NorthCoastModularCollective/Ann-Arbor-Percussion-Synthesizer/hardware/A2 Drums/A2 Drums.kicad_sch

## KiCad design hardware/A2 Drums/A2 Drums.kicad_sch (2023-11-15)

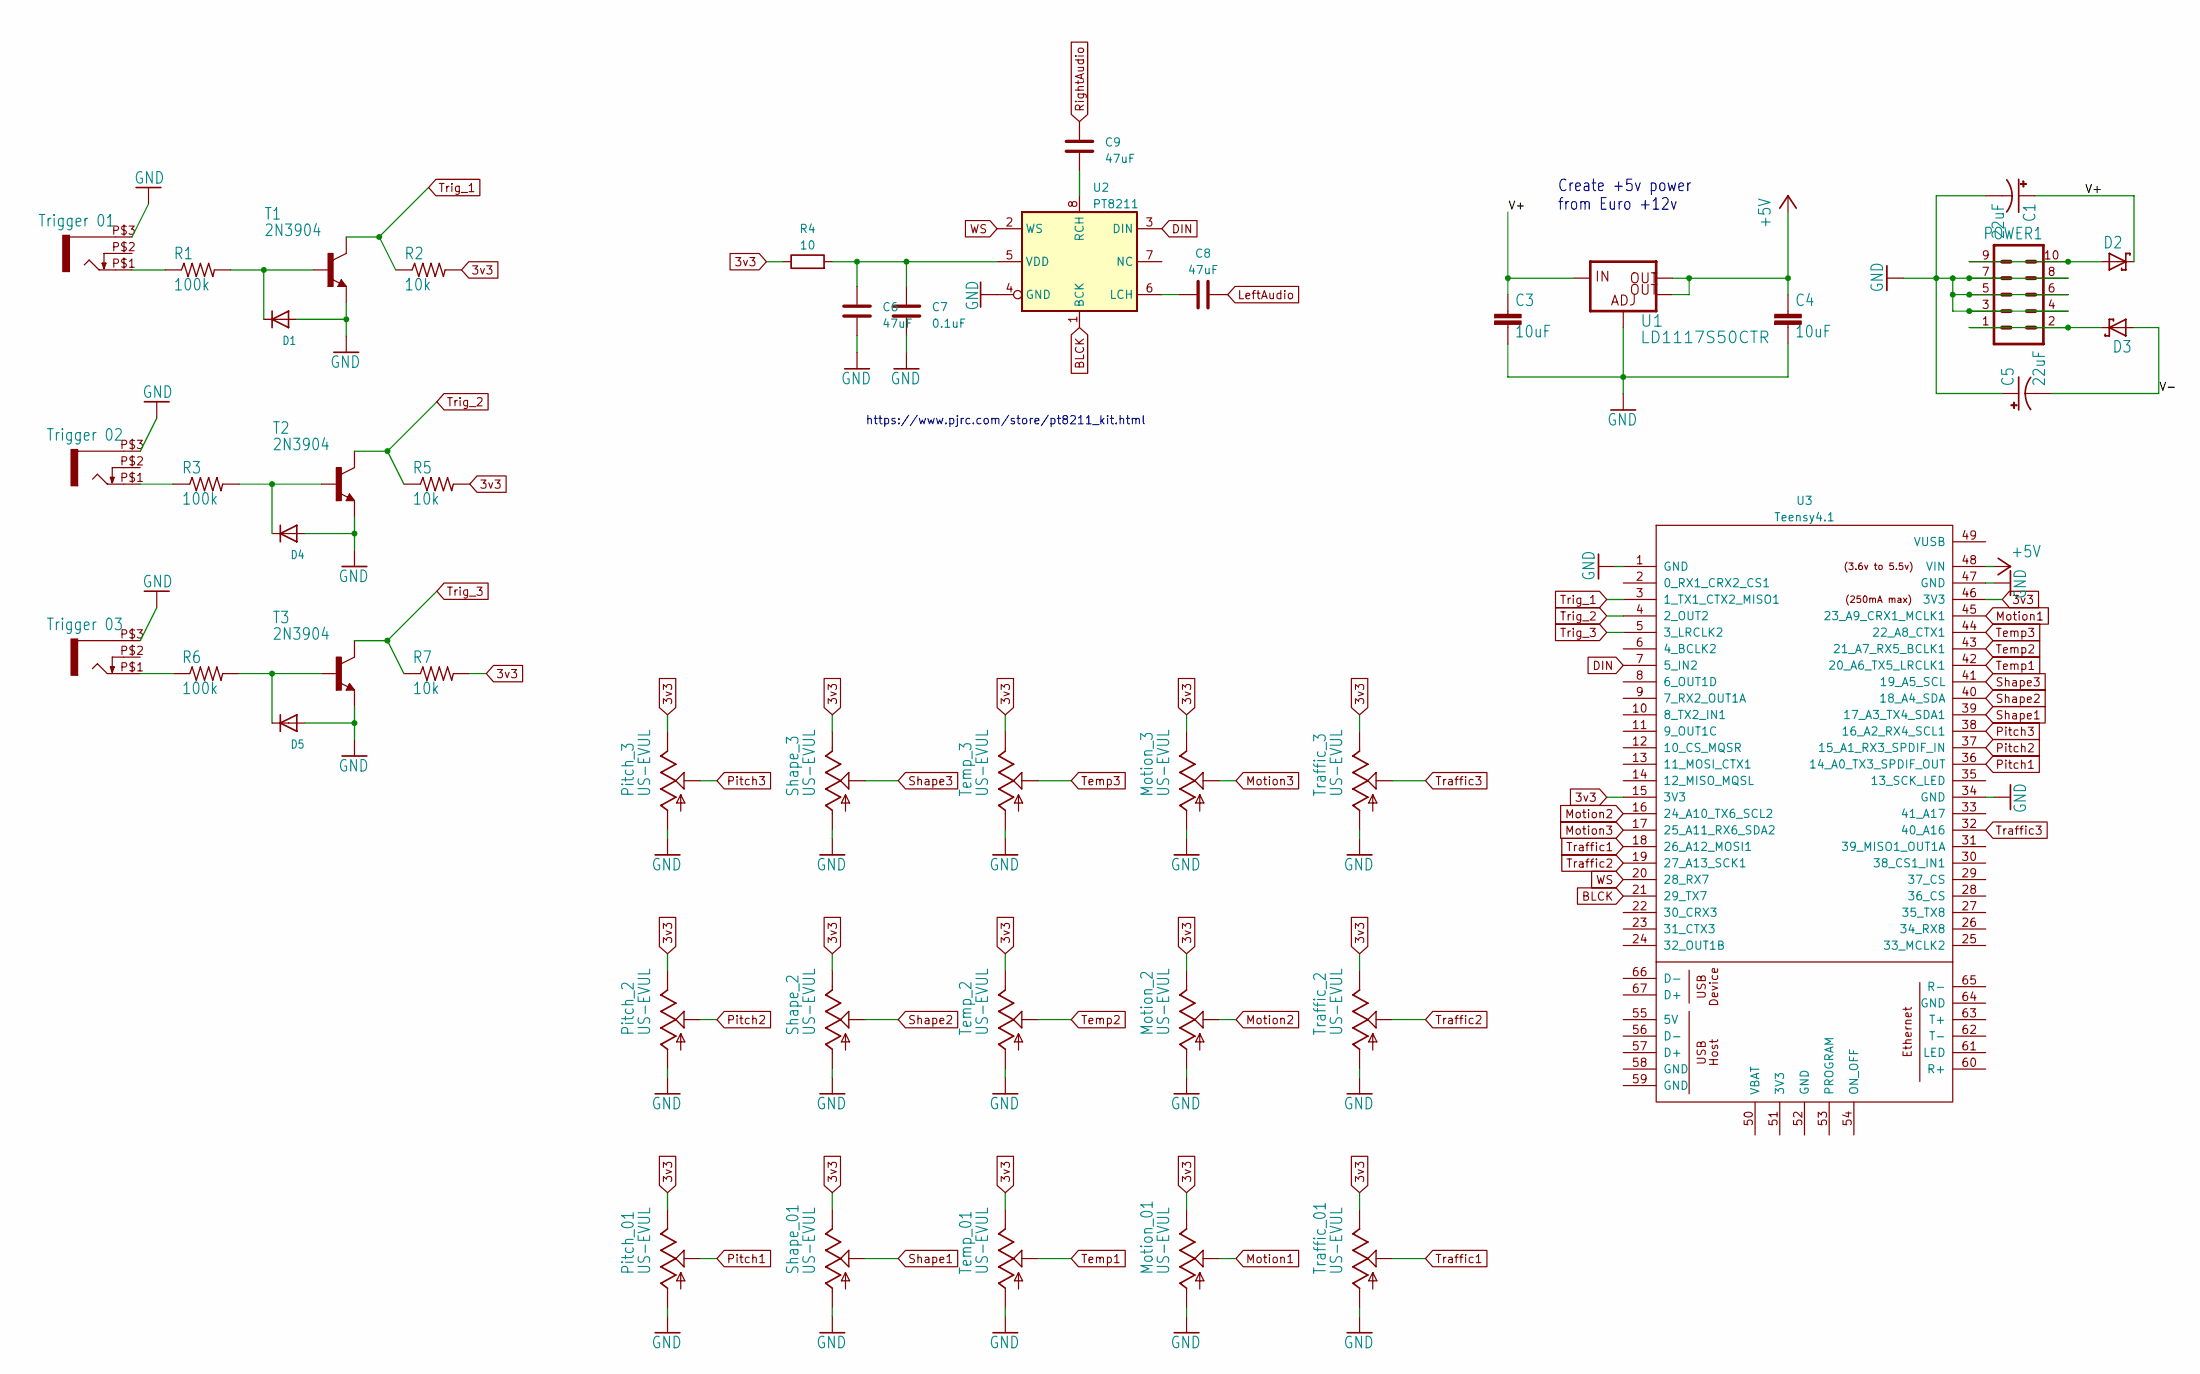
[picture p6: schematic A2 Drums.kicad_sch]

Parts:
C1, C5: 22uF; E2,5-5
C3, C4: 10uF; C5B2.5
C6, C8, C9: 47uF; C_Axial_L5.1mm_D3.1mm_P7.50mm_Horizontal
C7: 0.1uF; C_Axial_L5.1mm_D3.1mm_P7.50mm_Horizontal
D1, D4, D5: DIODESOD-123; SOD-123
D2, D3: SCHOTTKY-DIODEDO41; DO41-10
Motion_01, Motion_2, Motion_3: US-EVUL; EVUFXL
POWER1: MA05-2
Pitch_01, Pitch_2, Pitch_3: US-EVUL; EVUFXL
R1, R3, R6: 100k; R0805
R2, R5, R7: 10k; R0805
R4: 10; R_Axial_DIN0207_L6.3mm_D2.5mm_P7.62mm_Horizontal
Shape_01, Shape_2, Shape_3: US-EVUL; EVUFXL
T1, T2, T3: 2N3904; TO92
TRIG1: Trigger 01; WQP-PJ301M-12_JACK
TRIG2: Trigger 02; WQP-PJ301M-12_JACK
TRIG3: Trigger 03; WQP-PJ301M-12_JACK
Temp_01, Temp_2, Temp_3: US-EVUL; EVUFXL
Traffic_01, Traffic_2, Traffic_3: US-EVUL; EVUFXL
U1: LD1117S50CTR; SOT223
U2: PT8211; VSSOP-8_3.0x3.0mm_P0.65mm
U3: Teensy4.1

Connections:
3v3: Motion_01.3 (E), Motion_2.3 (E), Motion_3.3 (E), Pitch_01.3 (E), Pitch_2.3 (E), Pitch_3.3 (E), R2.2, R4.1, R5.2, R7.2, Shape_01.3 (E), Shape_2.3 (E), Shape_3.3 (E), Temp_01.3 (E), Temp_2.3 (E), Temp_3.3 (E), Traffic_01.3 (E), Traffic_2.3 (E), Traffic_3.3 (E), U3.15 (3V3), U3.46 (3V3)
+5V: C4.1, U1.2 (OUT), U1.4 (OUT@1), U3.48 (VIN)
BLCK: U2.1 (BCK), U3.21 (29_TX7)
DIN: U2.3 (DIN), U3.7 (5_IN2)
GND: C1.-, C3.2, C4.2, C5.+, C6.2, C7.2, D1.A, D4.A, D5.A, Motion_01.1 (A), Motion_2.1 (A), Motion_3.1 (A), POWER1.3, POWER1.4, POWER1.5, POWER1.6, POWER1.7, POWER1.8, Pitch_01.1 (A), Pitch_2.1 (A), Pitch_3.1 (A), Shape_01.1 (A), Shape_2.1 (A), Shape_3.1 (A), T1.3 (E), T2.3 (E), T3.3 (E), TRIG1.P$3 (1), TRIG2.P$3 (1), TRIG3.P$3 (1), Temp_01.1 (A), Temp_2.1 (A), Temp_3.1 (A), Traffic_01.1 (A), Traffic_2.1 (A), Traffic_3.1 (A), U1.1 (ADJ), U2.4 (GND), U3.1 (GND), U3.34 (GND), U3.47 (GND)
LeftAudio: C8.2
Motion1: Motion_01.2 (S), U3.45 (23_A9_CRX1_MCLK1)
Motion2: Motion_2.2 (S), U3.16 (24_A10_TX6_SCL2)
Motion3: Motion_3.2 (S), U3.17 (25_A11_RX6_SDA2)
unnamed: C6.1, C7.1, R4.2, U2.5 (VDD)
unnamed: C8.1, U2.6 (LCH)
unnamed: C9.1, U2.8 (RCH)
unnamed: D1.C, R1.2, T1.2 (B)
unnamed: D2.A, POWER1.9, POWER1.10
unnamed: D3.C, POWER1.1, POWER1.2
unnamed: D4.C, R3.2, T2.2 (B)
unnamed: D5.C, R6.2, T3.2 (B)
unnamed: R1.1, TRIG1.P$1 (2)
unnamed: R3.1, TRIG2.P$1 (2)
unnamed: R6.1, TRIG3.P$1 (2)
Pitch1: Pitch_01.2 (S), U3.36 (14_A0_TX3_SPDIF_OUT)
Pitch2: Pitch_2.2 (S), U3.37 (15_A1_RX3_SPDIF_IN)
Pitch3: Pitch_3.2 (S), U3.38 (16_A2_RX4_SCL1)
RightAudio: C9.2
Shape1: Shape_01.2 (S), U3.39 (17_A3_TX4_SDA1)
Shape2: Shape_2.2 (S), U3.40 (18_A4_SDA)
Shape3: Shape_3.2 (S), U3.41 (19_A5_SCL)
Temp1: Temp_01.2 (S), U3.42 (20_A6_TX5_LRCLK1)
Temp2: Temp_2.2 (S), U3.43 (21_A7_RX5_BCLK1)
Temp3: Temp_3.2 (S), U3.44 (22_A8_CTX1)
Traffic1: Traffic_01.2 (S), U3.18 (26_A12_MOSI1)
Traffic2: Traffic_2.2 (S), U3.19 (27_A13_SCK1)
Traffic3: Traffic_3.2 (S), U3.32 (40_A16)
Trig_1: R2.1, T1.1 (C), U3.3 (1_TX1_CTX2_MISO1)
Trig_2: R5.1, T2.1 (C), U3.4 (2_OUT2)
Trig_3: R7.1, T3.1 (C), U3.5 (3_LRCLK2)
V+: C1.+, C3.1, D2.C, U1.3 (IN)
V-: C5.-, D3.A
WS: U2.2 (WS), U3.20 (28_RX7)

Notes on the sheet:
Create +5v power from Euro +12v
https://www.pjrc.com/store/pt8211_kit.html
